dbrgn/sensilo/hardware/output/v1/screenshot.png

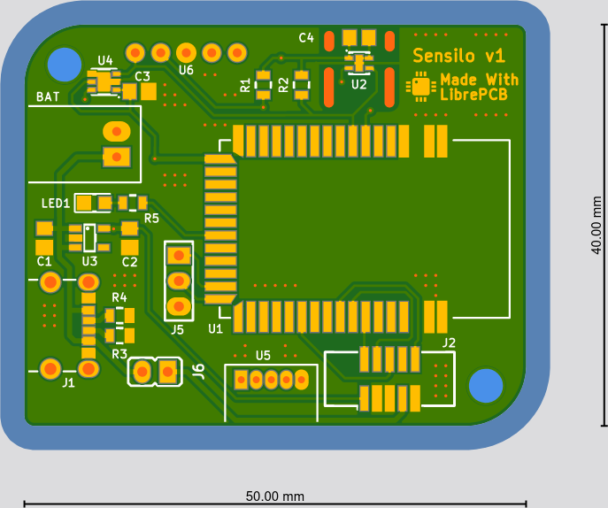
hardware/output/v1/screenshot.png
